MoltenZaz/Handwired-Kyria/Photos/IMG20230625232033.jpg

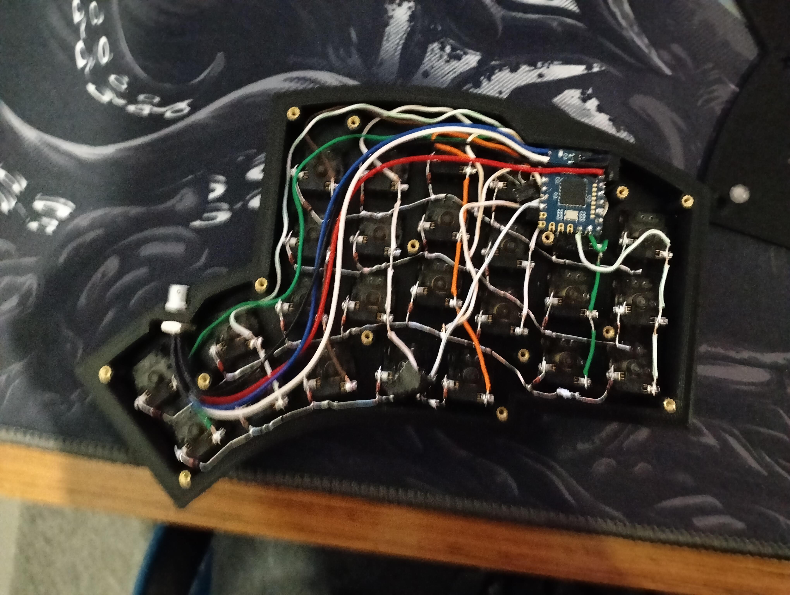
Photos/IMG20230625232033.jpg
