MoltenZaz/Handwired-Kyria/Photos/IMG20230626211425.jpg

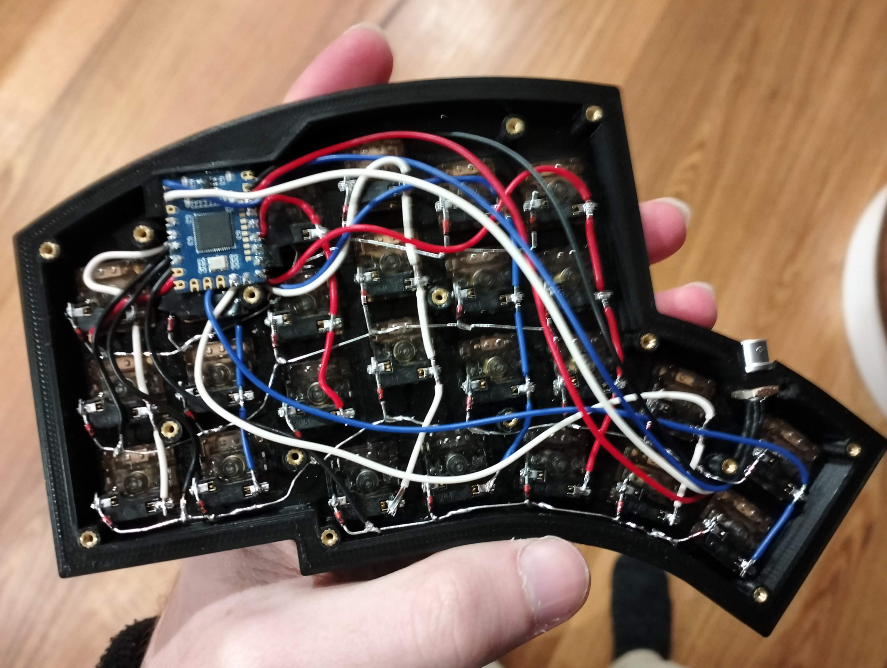
Photos/IMG20230626211425.jpg
