MoltenZaz/Handwired-Kyria/Photos/IMG20230628023117.jpg

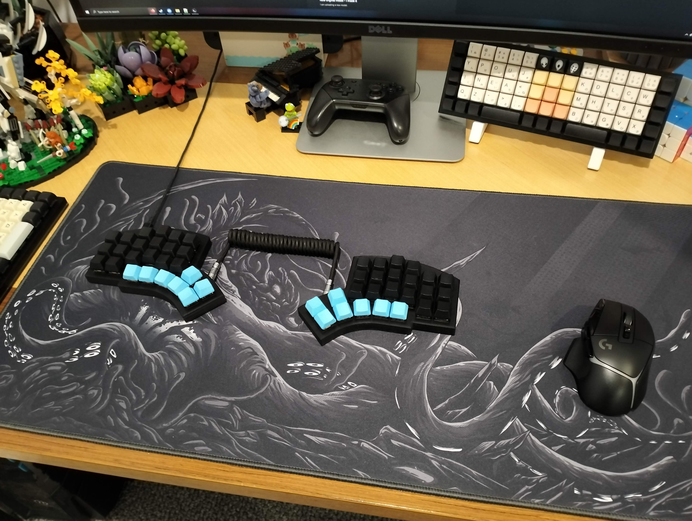
Photos/IMG20230628023117.jpg
