MoltenZaz/Handwired-Kyria/Photos/IMG20230628023246.jpg

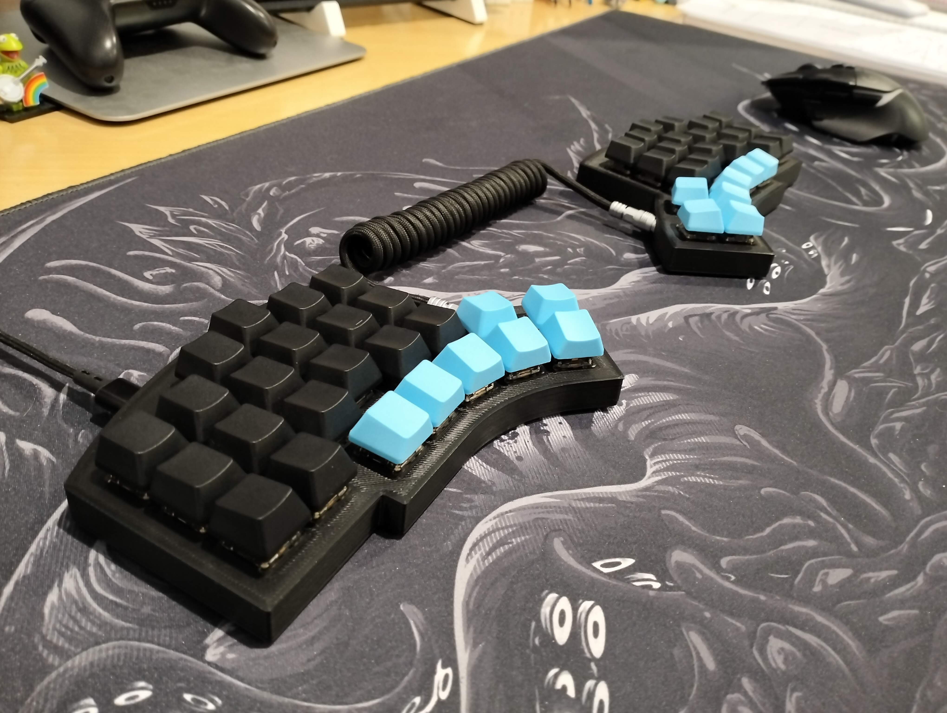
Photos/IMG20230628023246.jpg
