MoltenZaz/Handwired-Kyria/Photos/IMG20230628023303.jpg

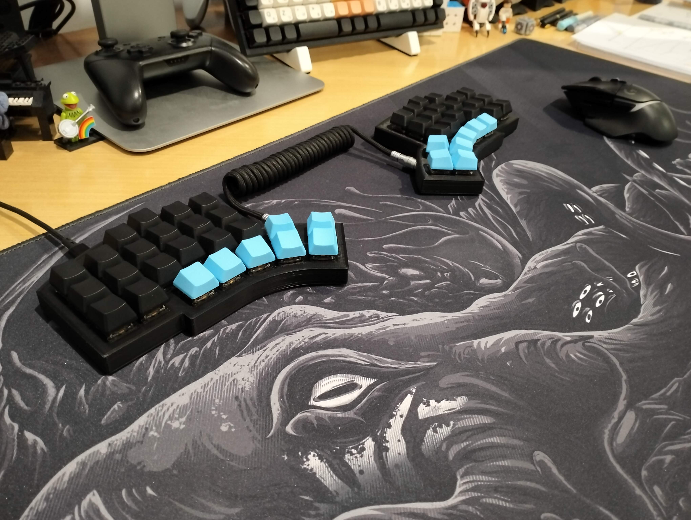
Photos/IMG20230628023303.jpg
